74hc595/Amethyst/include/note_numbers.h

/**
 * MIDI note numbers to be used with note().
 */
#ifndef NOTE_NUMBERS_H_
#define NOTE_NUMBERS_H_

enum note_number {
  /* MIDI notes 0-20 are outside the frequency range of the tone generator */
  NOTE_Am1  = 21,
  NOTE_Asm1 = 22,
  NOTE_Bm1  = 23,
  NOTE_C0   = 24,
  NOTE_Cs0  = 25,
  NOTE_D0   = 26,
  NOTE_Ds0  = 27,
  NOTE_E0   = 28,
  NOTE_F0   = 29,
  NOTE_Fs0  = 30,
  NOTE_G0   = 31,
  NOTE_Gs0  = 32,
  NOTE_A0   = 33,
  NOTE_As0  = 34,
  NOTE_B0   = 35,
  NOTE_C1   = 36,
  NOTE_Cs1  = 37,
  NOTE_D1   = 38,
  NOTE_Ds1  = 39,
  NOTE_E1   = 40,
  NOTE_F1   = 41,
  NOTE_Fs1  = 42,
  NOTE_G1   = 43,
  NOTE_Gs1  = 44,
  NOTE_A1   = 45,
  NOTE_As1  = 46,
  NOTE_B1   = 47,
  NOTE_C2   = 48,
  NOTE_Cs2  = 49,
  NOTE_D2   = 50,
  NOTE_Ds2  = 51,
  NOTE_E2   = 52,
  NOTE_F2   = 53,
  NOTE_Fs2  = 54,
  NOTE_G2   = 55,
  NOTE_Gs2  = 56,
  NOTE_A2   = 57,
  NOTE_As2  = 58,
  NOTE_B2   = 59,
  NOTE_C3   = 60,
  NOTE_Cs3  = 61,
  NOTE_D3   = 62,
  NOTE_Ds3  = 63,
  NOTE_E3   = 64,
  NOTE_F3   = 65,
  NOTE_Fs3  = 66,
  NOTE_G3   = 67,
  NOTE_Gs3  = 68,
  NOTE_A3   = 69,
  NOTE_As3  = 70,
  NOTE_B3   = 71,
  NOTE_C4   = 72,
  NOTE_Cs4  = 73,
  NOTE_D4   = 74,
  NOTE_Ds4  = 75,
  NOTE_E4   = 76,
  NOTE_F4   = 77,
  NOTE_Fs4  = 78,
  NOTE_G4   = 79,
  NOTE_Gs4  = 80,
  NOTE_A4   = 81,
  NOTE_As4  = 82,
  NOTE_B4   = 83,
  NOTE_C5   = 84,
  NOTE_Cs5  = 85,
  NOTE_D5   = 86,
  NOTE_Ds5  = 87,
  NOTE_E5   = 88,
  NOTE_F5   = 89,
  NOTE_Fs5  = 90,
  NOTE_G5   = 91,
  NOTE_Gs5  = 92,
  NOTE_A5   = 93,
  NOTE_As5  = 94,
  NOTE_B5   = 95,
  NOTE_C6   = 96,
  NOTE_Cs6  = 97,
  NOTE_D6   = 98,
  NOTE_Ds6  = 99,
  NOTE_E6   = 100,
  NOTE_F6   = 101,
  NOTE_Fs6  = 102,
  NOTE_G6   = 103,
  NOTE_Gs6  = 104,
  NOTE_A6   = 105,
  NOTE_As6  = 106,
  NOTE_B6   = 107,
  NOTE_C7   = 108,
  NOTE_Cs7  = 109,
  NOTE_D7   = 110,
  NOTE_Ds7  = 111,
  NOTE_E7   = 112,
  NOTE_F7   = 113,
  NOTE_Fs7  = 114,
  NOTE_G7   = 115,
  NOTE_Gs7  = 116,
  NOTE_A7   = 117,
  NOTE_As7  = 118,
  NOTE_B7   = 119,
  NOTE_C8   = 120,
  NOTE_Cs8  = 121,
  NOTE_D8   = 122,
  NOTE_Ds8  = 123,
  NOTE_E8   = 124,
  NOTE_F8   = 125,
  NOTE_Fs8  = 126,
  NOTE_G8   = 127,
};

#endif
